khaledmostafaismaiel/fighting_corona/Ven_des/right_side_for_assem.SLDPRT

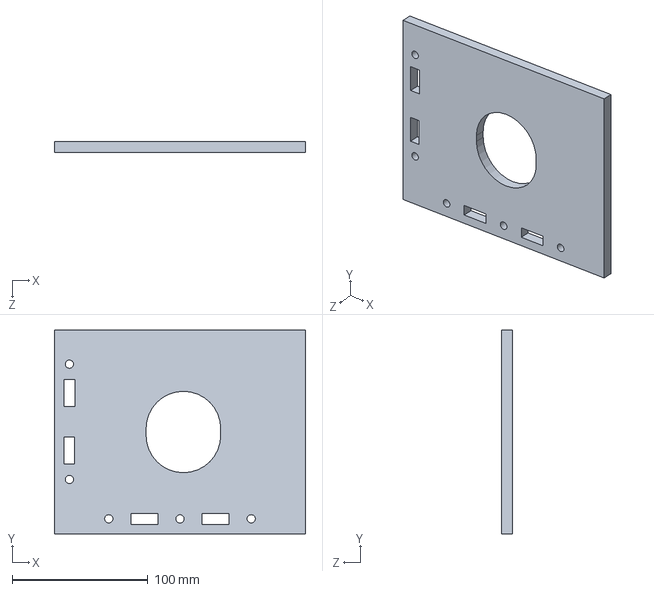
[picture p18: CAD file, 2020-04-04]
Ven_des/right_side_for_assem.SLDPRT
185.0 x 150.0 x 8.00 mm
