khaledmostafaismaiel/fighting_corona/Ven_des/hub_wire_for_assem.SLDPRT

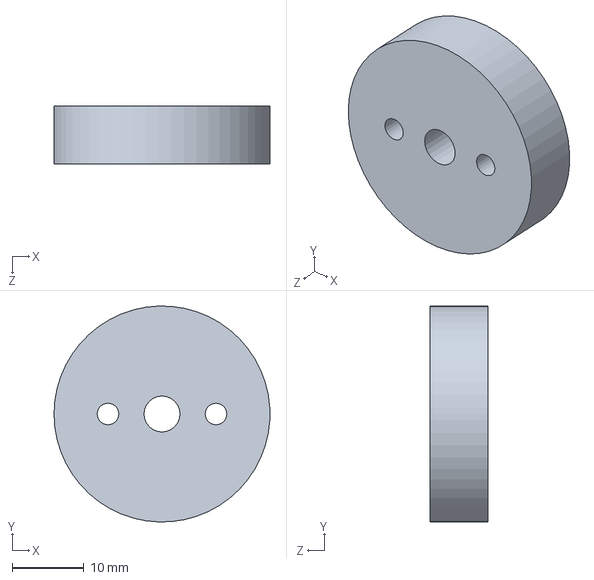
[picture p19: CAD file, 2020-04-04]
Ven_des/hub_wire_for_assem.SLDPRT
30.0 x 30.0 x 8.00 mm
