khaledmostafaismaiel/fighting_corona/Ven_des/bread_board_for_assem.SLDPRT

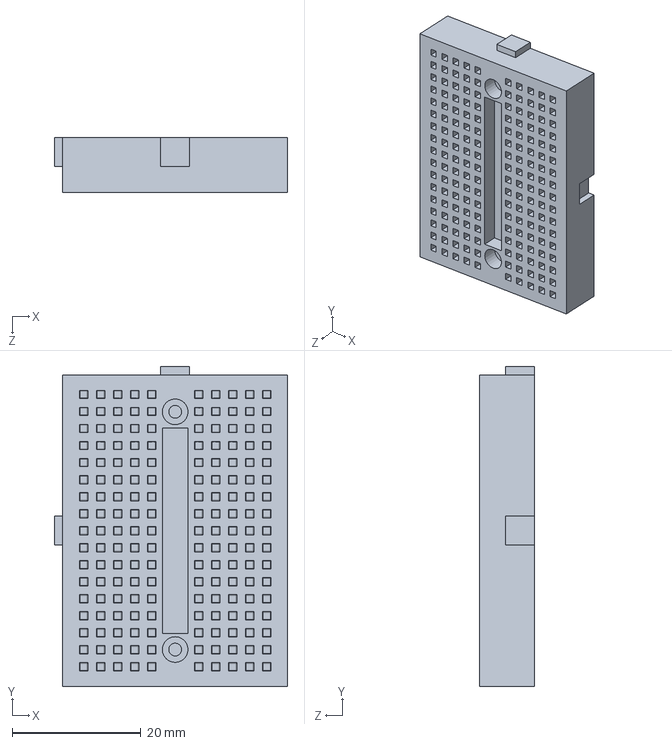
[picture p20: CAD file, 2020-04-04]
Ven_des/bread_board_for_assem.SLDPRT
36.3 x 49.8 x 8.50 mm
