khaledmostafaismaiel/fighting_corona/Ven_des/lcd_support_plat_for_assem.SLDPRT

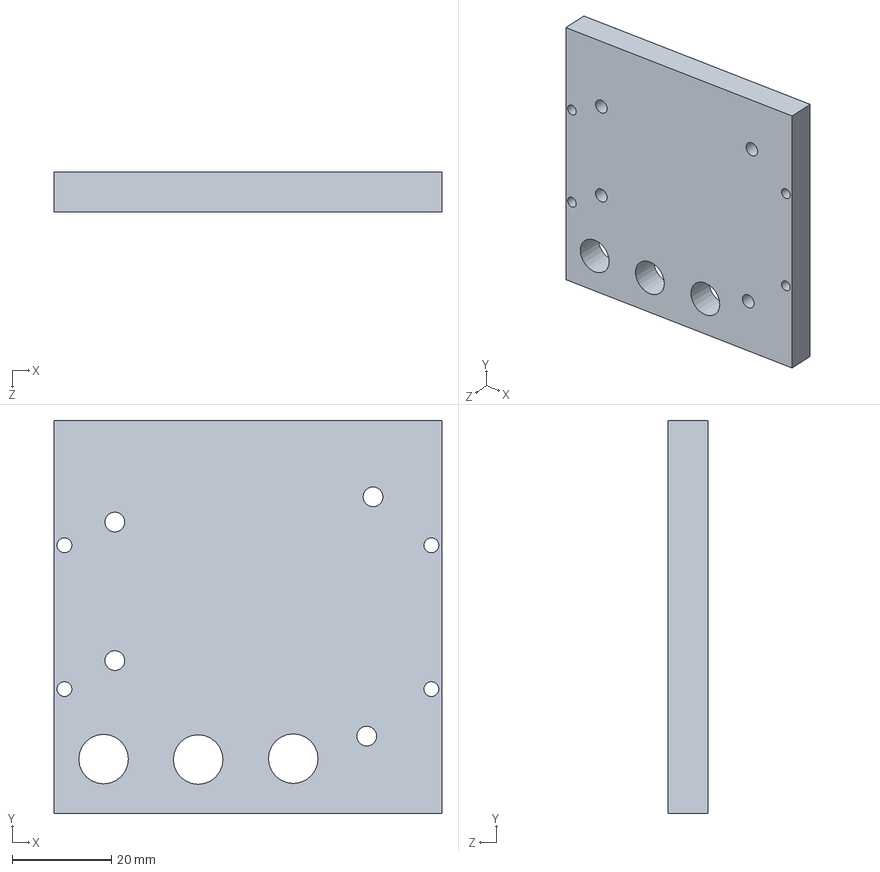
[picture p21: CAD file, 2020-04-04]
Ven_des/lcd_support_plat_for_assem.SLDPRT
78.2 x 79.3 x 8.00 mm
