khaledmostafaismaiel/fighting_corona/Ven_des/nema_17_for_assem.SLDPRT

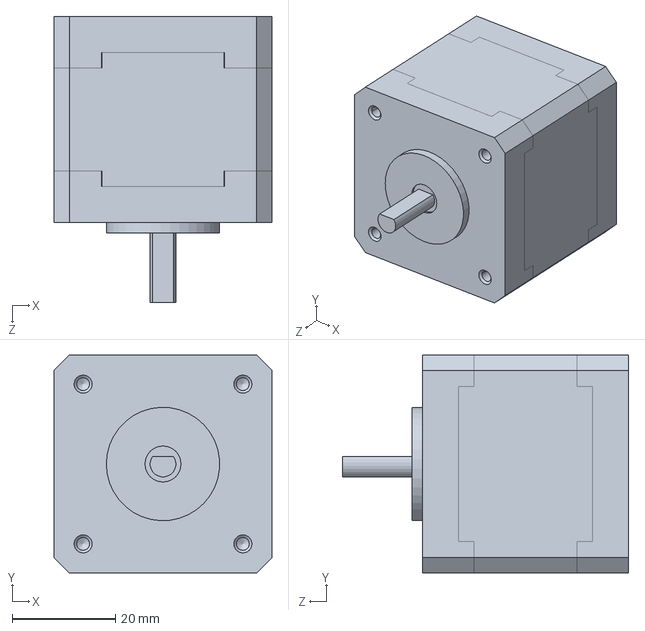
[picture p22: CAD file, 2020-04-04]
Ven_des/nema_17_for_assem.SLDPRT
42.3 x 42.3 x 55.5 mm
