khaledmostafaismaiel/fighting_corona/Ven_des/arm_for_assem.SLDPRT

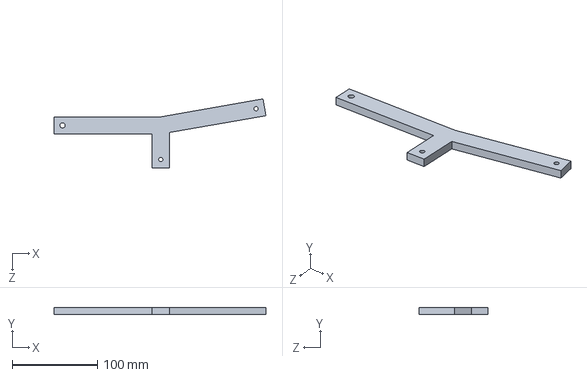
[picture p23: CAD file, 2020-04-04]
Ven_des/arm_for_assem.SLDPRT
248.2 x 8.00 x 81.1 mm
