khaledmostafaismaiel/fighting_corona/Ven_des/ambu_support_for_assem.SLDPRT

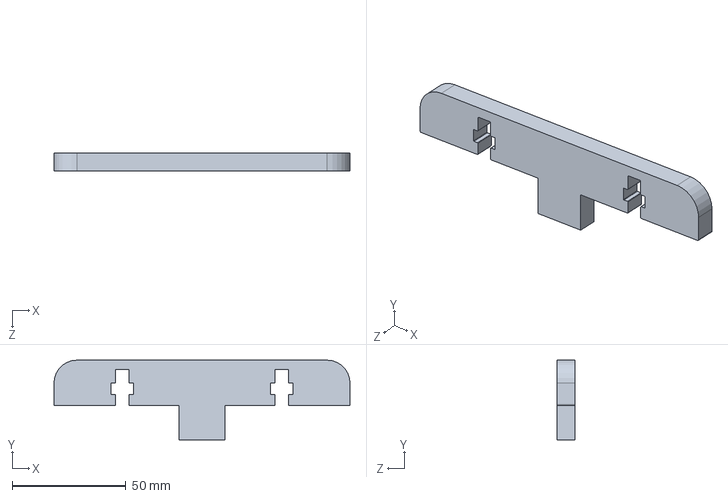
[picture p24: CAD file, 2020-04-04]
Ven_des/ambu_support_for_assem.SLDPRT
130.0 x 35.0 x 8.00 mm
