khaledmostafaismaiel/fighting_corona/Ven_des/arm_L_support_for_assem.SLDPRT

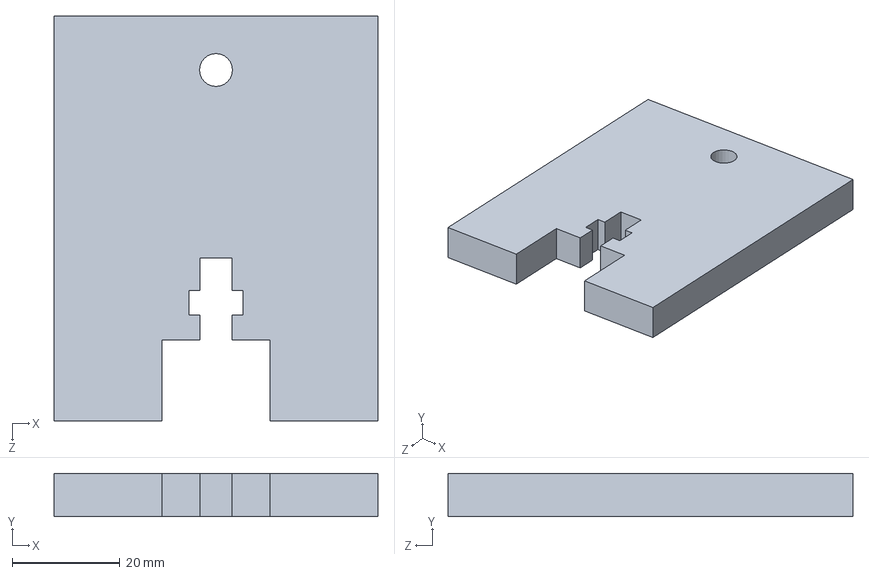
[picture p25: CAD file, 2020-04-04]
Ven_des/arm_L_support_for_assem.SLDPRT
60.0 x 8.00 x 75.0 mm
